slimakk/secured-vehicle-monitoring/Measurements/2023-05-21_18_19_influxdb_data.csv

#group | false | false | true | true | false | false | true | true
#datatype | string | long | dateTime:RFC3339 | dateTime:RFC3339 | dateTime:RFC3339 | double | string | string
#default | mean
 | result | table | _start | _stop | _time | _value | _field | _measurement
 |  | 0 | 2023-05-21T13:18:56.513924472Z | 2023-05-21T16:18:56.513924472Z | 2023-05-21T13:33:00Z | 29 | coolant_temp | OBD
 |  | 0 | 2023-05-21T13:18:56.513924472Z | 2023-05-21T16:18:56.513924472Z | 2023-05-21T13:34:00Z | 29 | coolant_temp | OBD
 |  | 0 | 2023-05-21T13:18:56.513924472Z | 2023-05-21T16:18:56.513924472Z | 2023-05-21T13:35:00Z | 29 | coolant_temp | OBD
 |  | 0 | 2023-05-21T13:18:56.513924472Z | 2023-05-21T16:18:56.513924472Z | 2023-05-21T13:36:00Z | 29 | coolant_temp | OBD
 |  | 0 | 2023-05-21T13:18:56.513924472Z | 2023-05-21T16:18:56.513924472Z | 2023-05-21T14:40:00Z | 28 | coolant_temp | OBD
 |  | 0 | 2023-05-21T13:18:56.513924472Z | 2023-05-21T16:18:56.513924472Z | 2023-05-21T14:41:00Z | 31.8 | coolant_temp | OBD
 |  | 0 | 2023-05-21T13:18:56.513924472Z | 2023-05-21T16:18:56.513924472Z | 2023-05-21T14:42:00Z | 46.4 | coolant_temp | OBD
 |  | 0 | 2023-05-21T13:18:56.513924472Z | 2023-05-21T16:18:56.513924472Z | 2023-05-21T14:43:00Z | 57.333333333333336 | coolant_temp | OBD
 |  | 0 | 2023-05-21T13:18:56.513924472Z | 2023-05-21T16:18:56.513924472Z | 2023-05-21T14:44:00Z | 65.6 | coolant_temp | OBD
 |  | 0 | 2023-05-21T13:18:56.513924472Z | 2023-05-21T16:18:56.513924472Z | 2023-05-21T14:45:00Z | 73.2 | coolant_temp | OBD
 |  | 0 | 2023-05-21T13:18:56.513924472Z | 2023-05-21T16:18:56.513924472Z | 2023-05-21T14:46:00Z | 79 | coolant_temp | OBD
 |  | 0 | 2023-05-21T13:18:56.513924472Z | 2023-05-21T16:18:56.513924472Z | 2023-05-21T14:47:00Z | 84.5 | coolant_temp | OBD
 |  | 0 | 2023-05-21T13:18:56.513924472Z | 2023-05-21T16:18:56.513924472Z | 2023-05-21T14:48:00Z | 89.8 | coolant_temp | OBD
 |  | 0 | 2023-05-21T13:18:56.513924472Z | 2023-05-21T16:18:56.513924472Z | 2023-05-21T14:49:00Z | 89.25 | coolant_temp | OBD
 |  | 0 | 2023-05-21T13:18:56.513924472Z | 2023-05-21T16:18:56.513924472Z | 2023-05-21T14:50:00Z | 87.8 | coolant_temp | OBD
 |  | 0 | 2023-05-21T13:18:56.513924472Z | 2023-05-21T16:18:56.513924472Z | 2023-05-21T14:51:00Z | 87.33333333333333 | coolant_temp | OBD
 |  | 0 | 2023-05-21T13:18:56.513924472Z | 2023-05-21T16:18:56.513924472Z | 2023-05-21T14:52:00Z | 87.33333333333333 | coolant_temp | OBD
 |  | 0 | 2023-05-21T13:18:56.513924472Z | 2023-05-21T16:18:56.513924472Z | 2023-05-21T14:53:00Z | 89 | coolant_temp | OBD
 |  | 0 | 2023-05-21T13:18:56.513924472Z | 2023-05-21T16:18:56.513924472Z | 2023-05-21T14:54:00Z | 88.8 | coolant_temp | OBD
 |  | 0 | 2023-05-21T13:18:56.513924472Z | 2023-05-21T16:18:56.513924472Z | 2023-05-21T14:55:00Z | 88.8 | coolant_temp | OBD
 |  | 0 | 2023-05-21T13:18:56.513924472Z | 2023-05-21T16:18:56.513924472Z | 2023-05-21T14:56:00Z | 91.33333333333333 | coolant_temp | OBD
 |  | 0 | 2023-05-21T13:18:56.513924472Z | 2023-05-21T16:18:56.513924472Z | 2023-05-21T14:57:00Z | 92 | coolant_temp | OBD
 |  | 0 | 2023-05-21T13:18:56.513924472Z | 2023-05-21T16:18:56.513924472Z | 2023-05-21T14:58:00Z | 93 | coolant_temp | OBD
 |  | 0 | 2023-05-21T13:18:56.513924472Z | 2023-05-21T16:18:56.513924472Z | 2023-05-21T14:59:00Z | 91.8 | coolant_temp | OBD
 |  | 0 | 2023-05-21T13:18:56.513924472Z | 2023-05-21T16:18:56.513924472Z | 2023-05-21T15:00:00Z | 90 | coolant_temp | OBD
 |  | 0 | 2023-05-21T13:18:56.513924472Z | 2023-05-21T16:18:56.513924472Z | 2023-05-21T15:01:00Z | 89.75 | coolant_temp | OBD
 |  | 0 | 2023-05-21T13:18:56.513924472Z | 2023-05-21T16:18:56.513924472Z | 2023-05-21T15:02:00Z | 90 | coolant_temp | OBD
 |  | 0 | 2023-05-21T13:18:56.513924472Z | 2023-05-21T16:18:56.513924472Z | 2023-05-21T15:03:00Z | 90 | coolant_temp | OBD
 |  | 0 | 2023-05-21T13:18:56.513924472Z | 2023-05-21T16:18:56.513924472Z | 2023-05-21T15:04:00Z | 90 | coolant_temp | OBD
 |  | 0 | 2023-05-21T13:18:56.513924472Z | 2023-05-21T16:18:56.513924472Z | 2023-05-21T15:05:00Z | 89.6 | coolant_temp | OBD
 |  | 0 | 2023-05-21T13:18:56.513924472Z | 2023-05-21T16:18:56.513924472Z | 2023-05-21T15:06:00Z | 90.33333333333333 | coolant_temp | OBD
 |  | 0 | 2023-05-21T13:18:56.513924472Z | 2023-05-21T16:18:56.513924472Z | 2023-05-21T15:07:00Z | 92.5 | coolant_temp | OBD
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
 |  | 2 | 2023-05-21T13:18:56.513924472Z | 2023-05-21T16:18:56.513924472Z | 2023-05-21T15:56:00Z | 53.4 | vehicle_speed | OBD
 |  | 2 | 2023-05-21T13:18:56.513924472Z | 2023-05-21T16:18:56.513924472Z | 2023-05-21T15:57:00Z | 46 | vehicle_speed | OBD
