slimakk/secured-vehicle-monitoring/Measurements/2023-06-09_14_13_influxdb_data.csv

#group | false | false | true | true | false | false | true | true
#datatype | string | long | dateTime:RFC3339 | dateTime:RFC3339 | dateTime:RFC3339 | double | string | string
#default | mean
 | result | table | _start | _stop | _time | _value | _field | _measurement
 |  | 0 | 2023-05-10T12:12:42.571693991Z | 2023-06-09T12:12:42.571693991Z | 2023-05-21T14:39:20Z | 4913.9652 | lat | location
 |  | 0 | 2023-05-10T12:12:42.571693991Z | 2023-06-09T12:12:42.571693991Z | 2023-05-21T14:39:25Z | 4913.9652 | lat | location
 |  | 0 | 2023-05-10T12:12:42.571693991Z | 2023-06-09T12:12:42.571693991Z | 2023-05-21T14:39:50Z | 4913.9652 | lat | location
 |  | 0 | 2023-05-10T12:12:42.571693991Z | 2023-06-09T12:12:42.571693991Z | 2023-05-21T14:40:05Z | 4913.9635 | lat | location
 |  | 0 | 2023-05-10T12:12:42.571693991Z | 2023-06-09T12:12:42.571693991Z | 2023-05-21T14:40:15Z | 4913.9636 | lat | location
 |  | 0 | 2023-05-10T12:12:42.571693991Z | 2023-06-09T12:12:42.571693991Z | 2023-05-21T14:40:30Z | 4913.9636 | lat | location
 |  | 0 | 2023-05-10T12:12:42.571693991Z | 2023-06-09T12:12:42.571693991Z | 2023-05-21T14:40:45Z | 4913.9636 | lat | location
 |  | 0 | 2023-05-10T12:12:42.571693991Z | 2023-06-09T12:12:42.571693991Z | 2023-05-21T14:40:50Z | 4913.9556 | lat | location
 |  | 0 | 2023-05-10T12:12:42.571693991Z | 2023-06-09T12:12:42.571693991Z | 2023-05-21T14:41:00Z | 4913.9556 | lat | location
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
 |  | 1 | 2023-05-10T12:12:42.571693991Z | 2023-06-09T12:12:42.571693991Z | 2023-05-21T15:55:20Z | 1630.2676 | lon | location
 |  | 1 | 2023-05-10T12:12:42.571693991Z | 2023-06-09T12:12:42.571693991Z | 2023-05-21T15:55:40Z | 1630.2676 | lon | location
 |  | 1 | 2023-05-10T12:12:42.571693991Z | 2023-06-09T12:12:42.571693991Z | 2023-05-21T15:55:50Z | 1630.2676 | lon | location
 |  | 1 | 2023-05-10T12:12:42.571693991Z | 2023-06-09T12:12:42.571693991Z | 2023-05-21T15:55:55Z | 1630.5488 | lon | location
 |  | 1 | 2023-05-10T12:12:42.571693991Z | 2023-06-09T12:12:42.571693991Z | 2023-05-21T15:56:10Z | 1630.5471 | lon | location
 |  | 1 | 2023-05-10T12:12:42.571693991Z | 2023-06-09T12:12:42.571693991Z | 2023-05-21T15:56:40Z | 1630.5471 | lon | location
