slimakk/secured-vehicle-monitoring/Schematic/new/final/iot_diagnostic_tool-car_comm.pdf

File: car.kicad_sch Sheet: /car_comm/ FEKT VUT GND

Id: 5/8 Title: OBD Monitoring Device
