slimakk/secured-vehicle-monitoring/Schematic/new/final/iot_diagnostic_tool-connectors.pdf

File: connect.kicad_sch Sheet: /connectors/ FEKT VUT

Id: 4/8 Title: OBD Monitoring Device
