slimakk/secured-vehicle-monitoring/Schematic/new/final/iot_diagnostic_tool-iot_module-antenna.pdf

File: ant.kicad_sch Sheet: /iot_module/antenna/ FEKT VUT C40 NM

Id: 8/8 Title: OBD Monitoring Device
