slimakk/secured-vehicle-monitoring/Schematic/new/final/iot_diagnostic_tool-iot_module-sim.pdf

Id: 6/8 Title: OBD Monitoring Device
