slimakk/secured-vehicle-monitoring/Schematic/new/final/iot_diagnostic_tool-iot_module-usb.pdf

File: usb.kicad_sch Sheet: /iot_module/usb/ FEKT VUT

Id: 7/8 Title: OBD Monitoring Device
