slimakk/secured-vehicle-monitoring/Schematic/new/final/iot_diagnostic_tool-iot_module.pdf

File: iot.kicad_sch Sheet: /iot_module/ FEKT VUT

Id: 3/8 Title: OBD Monitoring Device
