slimakk/secured-vehicle-monitoring/Schematic/new/final/iot_diagnostic_tool-power_supply.pdf

File: pwr.kicad_sch Sheet: /power_supply/ FEKT VUT

Id: 2/8 Title: OBD Monitoring Device
