slimakk/secured-vehicle-monitoring/Schematic/new/new_layout.pdf

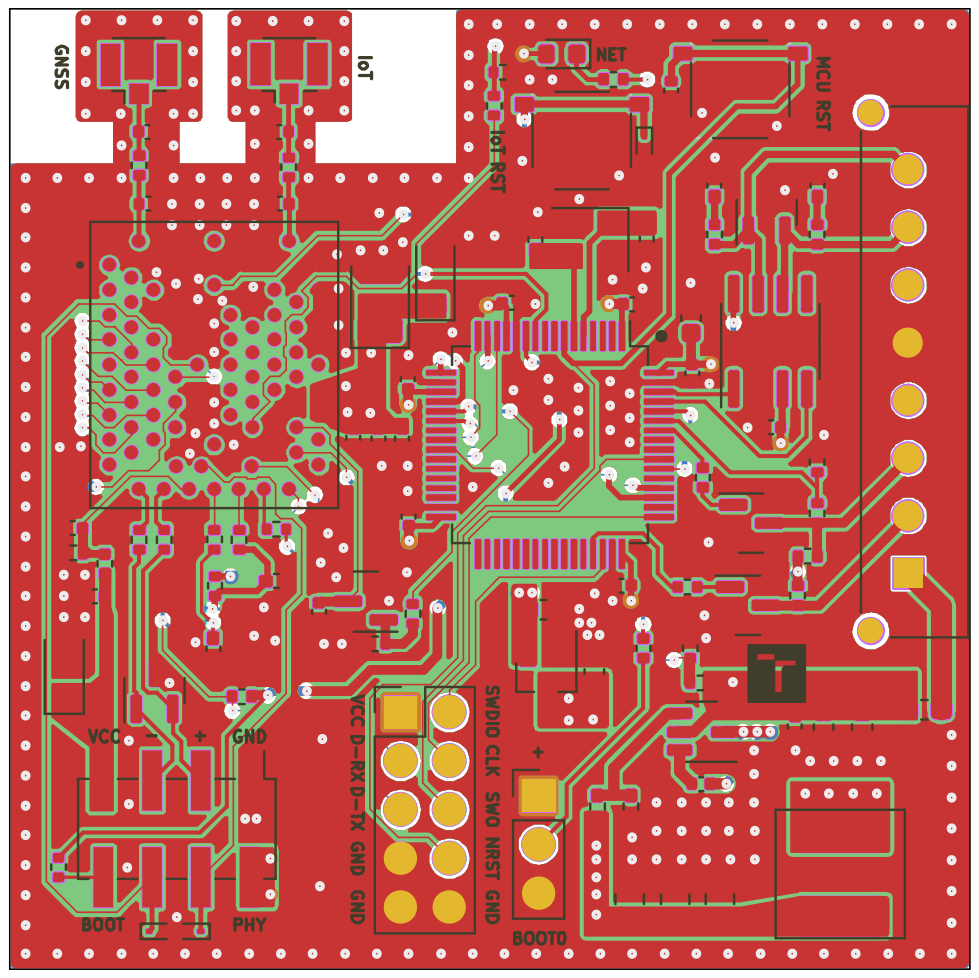
[picture p37: page 1]
