slimakk/secured-vehicle-monitoring/Schematic/new/new_layout_cut.pdf

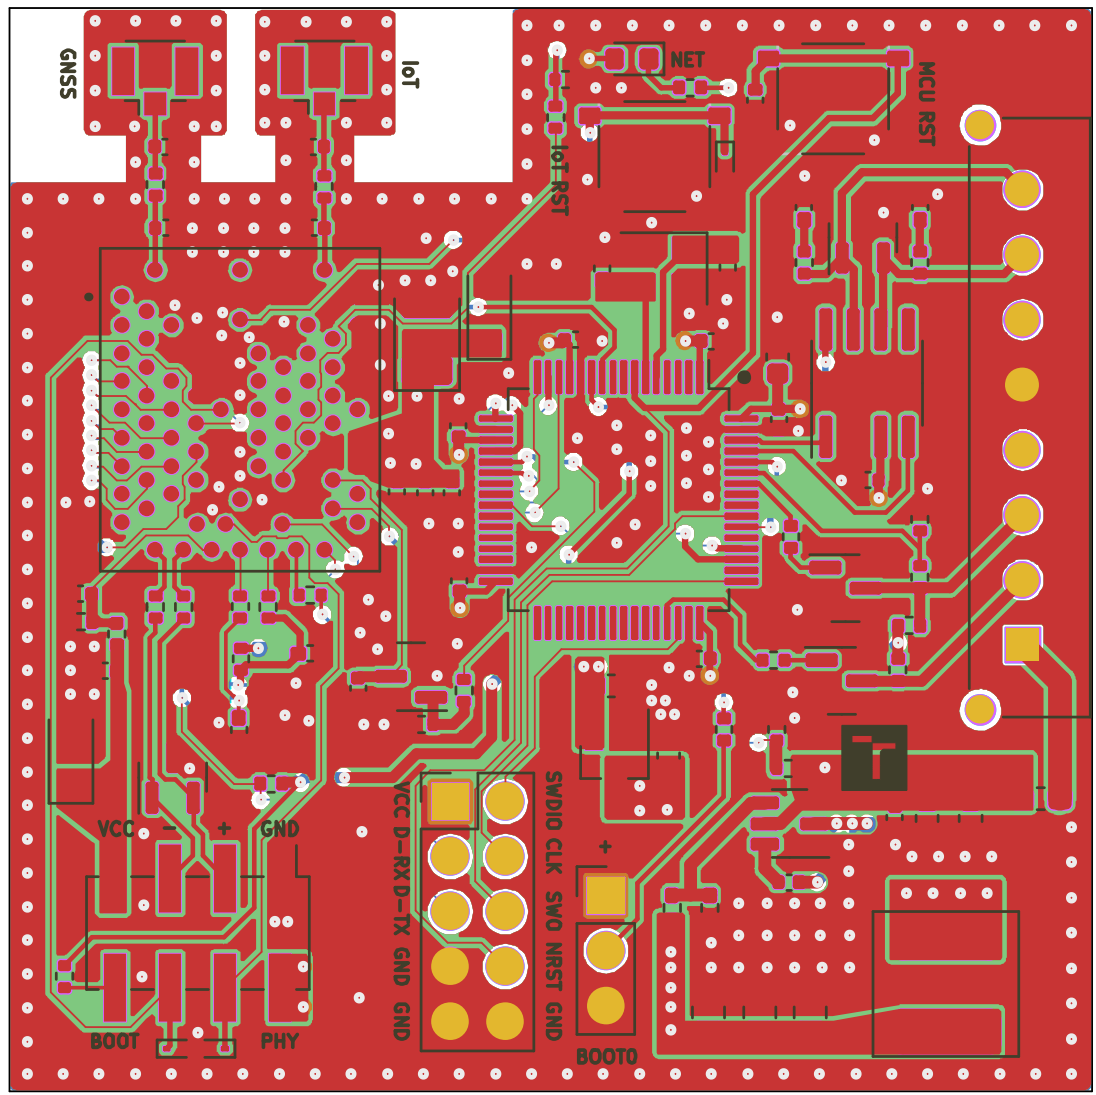
[picture p38: page 1]
