slimakk/secured-vehicle-monitoring/Schematic/new/pontrig.pdf

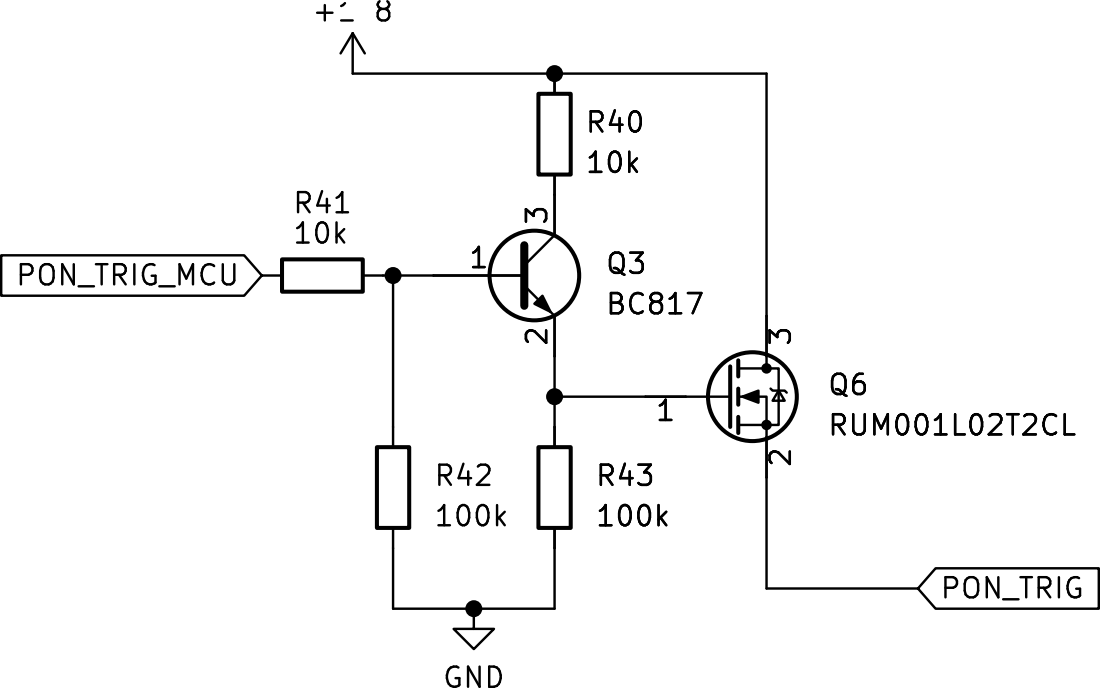
[picture p39: page 1]
