slimakk/secured-vehicle-monitoring/Schematic/new/pwr.pdf

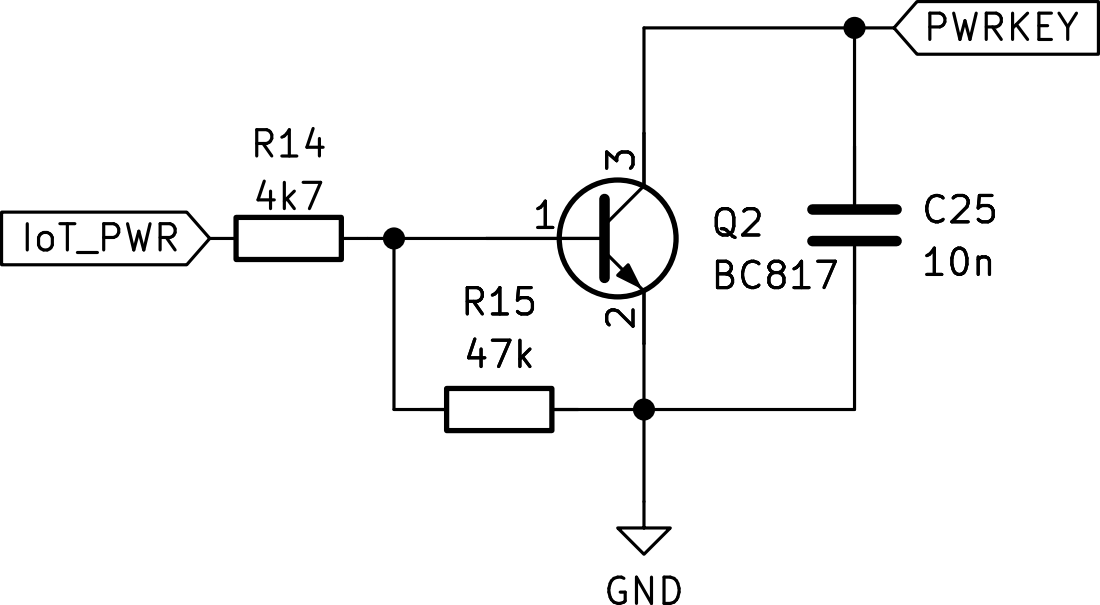
[picture p40: page 1]
