slimakk/secured-vehicle-monitoring/Schematic/new/pwr_sup.pdf

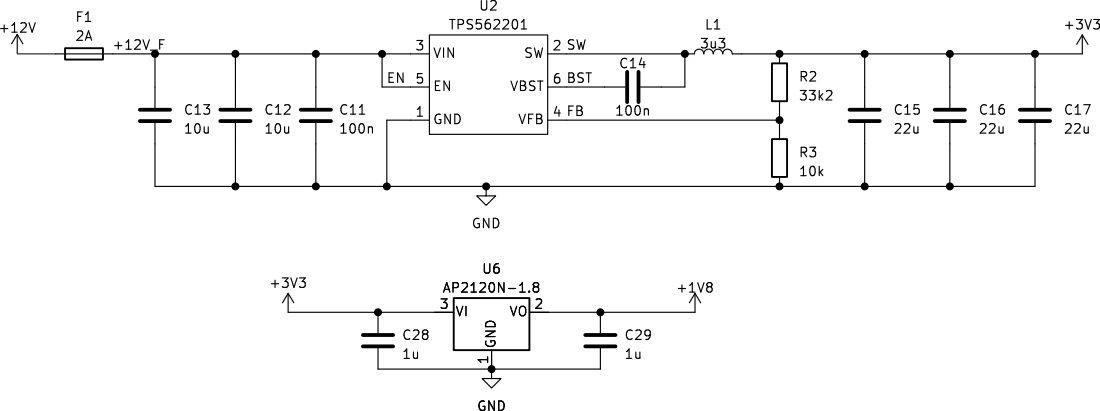
[picture p41: page 1]
