slimakk/secured-vehicle-monitoring/Schematic/new/sim.pdf

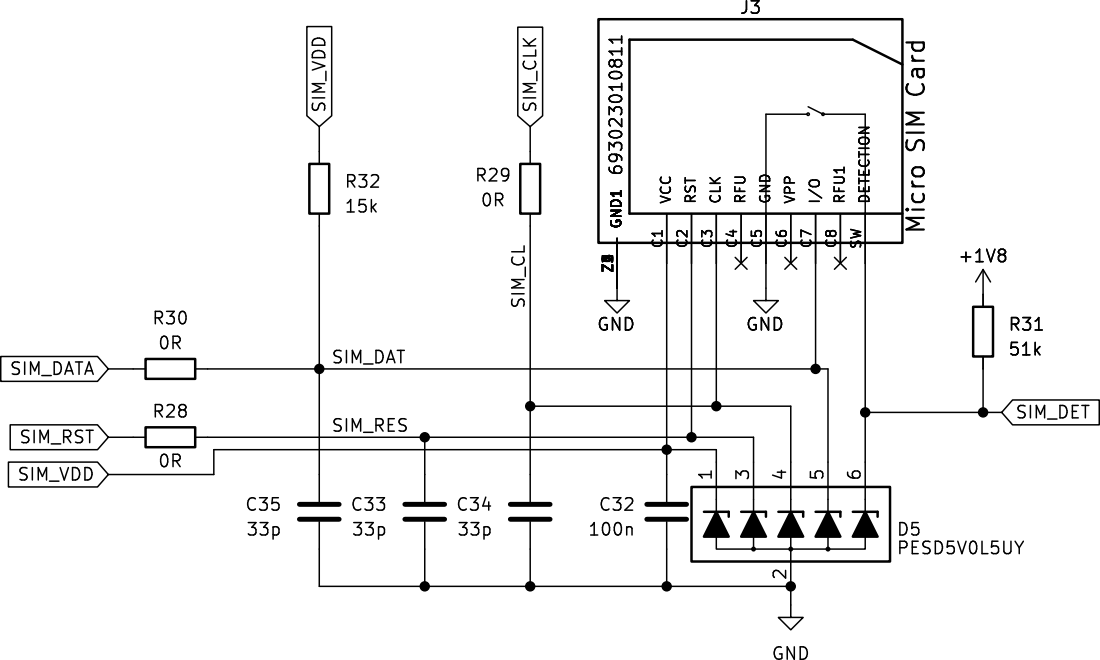
[picture p42: page 1]
