slimakk/secured-vehicle-monitoring/Schematic/new/usb.pdf

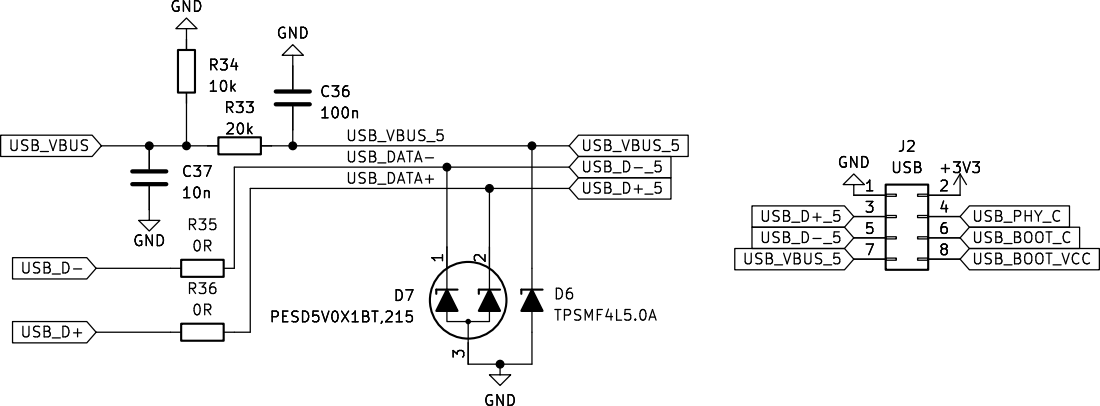
[picture p43: page 1]
