slimakk/secured-vehicle-monitoring/Schematic/part/stm_v3-Power Supply.pdf

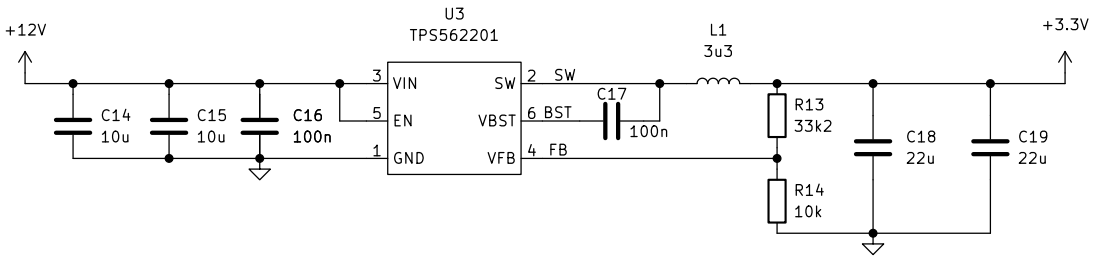
[picture p44: page 1]
