slimakk/secured-vehicle-monitoring/Schematic/schema_v1.pdf

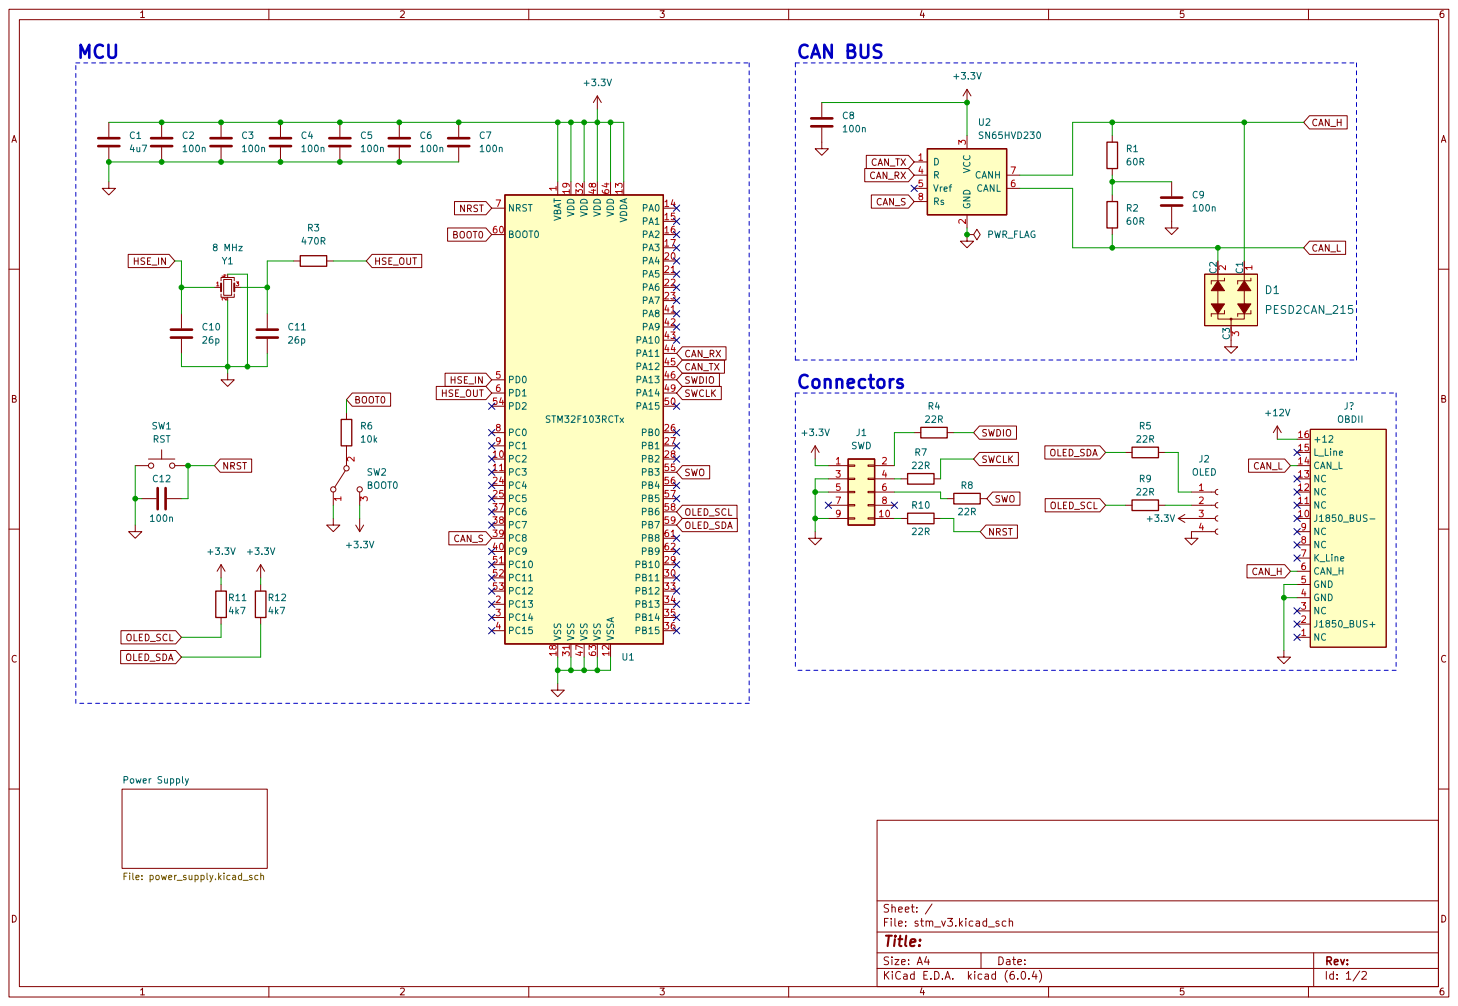
[picture p45: page 1]

1 PC2 10 PC3 11 VSSA 12 VDDA 13 PA0 14 PA1 15 PA2 16 PA3 17 VSS 18 VDD 19 PC13 2 PA4 20 PA5 21 PA6 22 PA7 23 PC4 24 PC5 25 PB0 26 PB1 27 PB2 28 PB10 29 PC14 3 PB11 30 VSS 31 VDD 32 PB12 33 PB13 34 PB14 35 PB15 36 PC6 37 PC7 38 PC8 39 PC15 4 PC9 40 PA8 41 PA9 42 PA10 43 PA11 44 PA12 45 PA13 46 VSS 47 VDD 48 PA14 49 PD0 5 PA15 50 PC10 51 PC11 52 PC12 53 PD2 54 PB3 55 PB4 56 PB5 57 PB6 58 PB7 59 PD1 6 BOOT0 60 PB8 61 PB9 62 VSS 63 VDD 64 NRST 7 PC0 8 PC1 9 U1 STM32F103RCTx PWR_FLAG

File: stm_v3.kicad_sch Sheet: / Power Supply

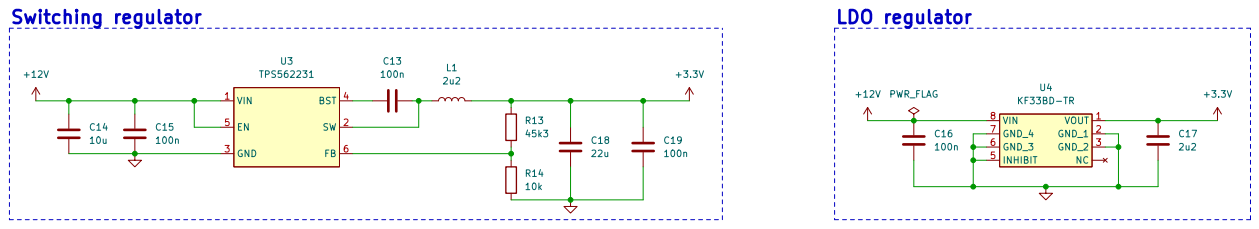
[picture p46: page 2]
