slimakk/secured-vehicle-monitoring/iot_obd_monitoring_device/Core/Src/tim.c

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
/* Includes ------------------------------------------------------------------*/
#include "tim.h"

/* USER CODE BEGIN 0 */
extern OBD obd_comm;
extern BG77 module;
/* USER CODE END 0 */

TIM_HandleTypeDef htim6;
TIM_HandleTypeDef htim7;
TIM_HandleTypeDef htim16;

/* TIM6 init function */
void MX_TIM6_Init(void)
{

  TIM_MasterConfigTypeDef sMasterConfig = {0};

  htim6.Instance = TIM6;
  htim6.Init.Prescaler = 800;
  htim6.Init.CounterMode = TIM_COUNTERMODE_UP;
  htim6.Init.Period = 8000;
  htim6.Init.AutoReloadPreload = TIM_AUTORELOAD_PRELOAD_DISABLE;
  if (HAL_TIM_Base_Init(&htim6) != HAL_OK)
  {
    Error_Handler();
  }
  sMasterConfig.MasterOutputTrigger = TIM_TRGO_RESET;
  sMasterConfig.MasterSlaveMode = TIM_MASTERSLAVEMODE_DISABLE;
  if (HAL_TIMEx_MasterConfigSynchronization(&htim6, &sMasterConfig) != HAL_OK)
  {
    Error_Handler();
  }
}
/* TIM7 init function */
void MX_TIM7_Init(void)
{

  TIM_MasterConfigTypeDef sMasterConfig = {0};

  htim7.Instance = TIM7;
  htim7.Init.Prescaler = 39999;
  htim7.Init.CounterMode = TIM_COUNTERMODE_UP;
  htim7.Init.Period = 1999;
  htim7.Init.AutoReloadPreload = TIM_AUTORELOAD_PRELOAD_DISABLE;
  if (HAL_TIM_Base_Init(&htim7) != HAL_OK)
  {
    Error_Handler();
  }
  sMasterConfig.MasterOutputTrigger = TIM_TRGO_RESET;
  sMasterConfig.MasterSlaveMode = TIM_MASTERSLAVEMODE_DISABLE;
  if (HAL_TIMEx_MasterConfigSynchronization(&htim7, &sMasterConfig) != HAL_OK)
  {
    Error_Handler();
  }
}
/* TIM16 init function */
void MX_TIM16_Init(void)
{

  htim16.Instance = TIM16;
  htim16.Init.Prescaler = 39999;
  htim16.Init.CounterMode = TIM_COUNTERMODE_UP;
  htim16.Init.Period = 3999;
  htim16.Init.ClockDivision = TIM_CLOCKDIVISION_DIV1;
  htim16.Init.RepetitionCounter = 0;
  htim16.Init.AutoReloadPreload = TIM_AUTORELOAD_PRELOAD_DISABLE;
  if (HAL_TIM_Base_Init(&htim16) != HAL_OK)
  {
    Error_Handler();
  }
}

void HAL_TIM_Base_MspInit(TIM_HandleTypeDef* tim_baseHandle)
{

  if(tim_baseHandle->Instance==TIM6)
  {
    /* TIM6 clock enable */
    __HAL_RCC_TIM6_CLK_ENABLE();

    /* TIM6 interrupt Init */
    HAL_NVIC_SetPriority(TIM6_DAC_IRQn, 2, 0);
    HAL_NVIC_EnableIRQ(TIM6_DAC_IRQn);
  }
  else if(tim_baseHandle->Instance==TIM7)
  {
    /* TIM7 clock enable */
    __HAL_RCC_TIM7_CLK_ENABLE();

    /* TIM7 interrupt Init */
    HAL_NVIC_SetPriority(TIM7_IRQn, 2, 0);
    HAL_NVIC_EnableIRQ(TIM7_IRQn);
  }
  else if(tim_baseHandle->Instance==TIM16)
  {
    /* TIM16 clock enable */
    __HAL_RCC_TIM16_CLK_ENABLE();

    /* TIM16 interrupt Init */
    HAL_NVIC_SetPriority(TIM1_UP_TIM16_IRQn, 2, 0);
    HAL_NVIC_EnableIRQ(TIM1_UP_TIM16_IRQn);
  }
}

void HAL_TIM_Base_MspDeInit(TIM_HandleTypeDef* tim_baseHandle)
{

  if(tim_baseHandle->Instance==TIM6)
  {
    /* Peripheral clock disable */
    __HAL_RCC_TIM6_CLK_DISABLE();

    /* TIM6 interrupt Deinit */
    HAL_NVIC_DisableIRQ(TIM6_DAC_IRQn);
  }
  else if(tim_baseHandle->Instance==TIM7)
  {
    /* Peripheral clock disable */
    __HAL_RCC_TIM7_CLK_DISABLE();

    /* TIM7 interrupt Deinit */
    HAL_NVIC_DisableIRQ(TIM7_IRQn);
  }
  else if(tim_baseHandle->Instance==TIM16)
  {
    /* Peripheral clock disable */
    __HAL_RCC_TIM16_CLK_DISABLE();

    /* TIM16 interrupt Deinit */
    HAL_NVIC_DisableIRQ(TIM1_UP_TIM16_IRQn);
  }
}

/* USER CODE BEGIN 1 */
void HAL_TIM_PeriodElapsedCallback(TIM_HandleTypeDef *htim)
{
	if (htim->Instance == TIM2)
	{
	    HAL_IncTick();
	}
	if(htim->Instance == TIM6)
	{
		if(obd_comm.msg_type == 0)
		{
			__NOP();
		}
		else
		{
			obd_comm.msg_type = 3;
		}
		HAL_TIM_Base_Stop_IT(htim);
	}
	else if(htim->Instance == TIM7)
	{
		module.received = 1;
		HAL_TIM_Base_Stop_IT(htim);
	}
	else if(htim->Instance == TIM16)
	{
		obd_comm.timeout = 1;
		HAL_TIM_Base_Stop_IT(htim);
	}
}


/* USER CODE END 1 */
