slimakk/secured-vehicle-monitoring/iot_obd_monitoring_device/Core/Src/OBD/can.c

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
/* Includes ------------------------------------------------------------------*/
#include "can.h"
#include "OBD.h"
/* USER CODE BEGIN 0 */
extern OBD obd_comm;
//extern IWDG_HandleTypeDef hiwdg;
uint32_t tx_mailbox;
uint8_t rx_mailbox[RX_DATA_LENGTH];

/* USER CODE END 0 */

CAN_HandleTypeDef hcan1;

/* CAN1 init function */
void MX_CAN1_Init(void)
{

  hcan1.Instance = CAN1;
  hcan1.Init.Prescaler = 16;
  hcan1.Init.Mode = CAN_MODE_NORMAL;
  hcan1.Init.SyncJumpWidth = CAN_SJW_1TQ;
  hcan1.Init.TimeSeg1 = CAN_BS1_8TQ;
  hcan1.Init.TimeSeg2 = CAN_BS2_1TQ;
  hcan1.Init.TimeTriggeredMode = DISABLE;
  hcan1.Init.AutoBusOff = DISABLE;
  hcan1.Init.AutoWakeUp = DISABLE;
  hcan1.Init.AutoRetransmission = DISABLE;
  hcan1.Init.ReceiveFifoLocked = DISABLE;
  hcan1.Init.TransmitFifoPriority = DISABLE;
  if (HAL_CAN_Init(&hcan1) != HAL_OK)
  {
    Error_Handler();
  }
}

void HAL_CAN_MspInit(CAN_HandleTypeDef* canHandle)
{

  GPIO_InitTypeDef GPIO_InitStruct = {0};
  if(canHandle->Instance==CAN1)
  {
    /* CAN1 clock enable */
    __HAL_RCC_CAN1_CLK_ENABLE();

    __HAL_RCC_GPIOB_CLK_ENABLE();
    /**CAN1 GPIO Configuration
    PB8     ------> CAN1_RX
    PB9     ------> CAN1_TX
    */
    GPIO_InitStruct.Pin = GPIO_PIN_8|GPIO_PIN_9;
    GPIO_InitStruct.Mode = GPIO_MODE_AF_PP;
    GPIO_InitStruct.Pull = GPIO_NOPULL;
    GPIO_InitStruct.Speed = GPIO_SPEED_FREQ_VERY_HIGH;
    GPIO_InitStruct.Alternate = GPIO_AF9_CAN1;
    HAL_GPIO_Init(GPIOB, &GPIO_InitStruct);

    /* CAN1 interrupt Init */
    HAL_NVIC_SetPriority(CAN1_RX0_IRQn, 0, 0);
    HAL_NVIC_EnableIRQ(CAN1_RX0_IRQn);
    HAL_NVIC_SetPriority(CAN1_RX1_IRQn, 0, 0);
    HAL_NVIC_EnableIRQ(CAN1_RX1_IRQn);
  }
}

void HAL_CAN_MspDeInit(CAN_HandleTypeDef* canHandle)
{

  if(canHandle->Instance==CAN1)
  {
    /* Peripheral clock disable */
    __HAL_RCC_CAN1_CLK_DISABLE();

    /**CAN1 GPIO Configuration
    PB8     ------> CAN1_RX
    PB9     ------> CAN1_TX
    */
    HAL_GPIO_DeInit(GPIOB, GPIO_PIN_8|GPIO_PIN_9);

    /* CAN1 interrupt Deinit */
    HAL_NVIC_DisableIRQ(CAN1_RX0_IRQn);
    HAL_NVIC_DisableIRQ(CAN1_RX1_IRQn);
  }
}

/* USER CODE BEGIN 1 */
void can_config(void)
{
	CAN_FilterTypeDef can_filter;
	can_filter.FilterBank = 0;
	can_filter.FilterMode = CAN_FILTERMODE_IDMASK;
	can_filter.FilterScale = CAN_FILTERSCALE_32BIT;
	can_filter.FilterIdHigh = 0x7E8 << 5;
	can_filter.FilterIdLow = 0x0000;
	can_filter.FilterMaskIdHigh = 0x7F8 << 5;
	can_filter.FilterMaskIdLow = 0x0000;
	can_filter.FilterFIFOAssignment = CAN_RX_FIFO0;
	can_filter.FilterActivation = ENABLE;

	if(HAL_CAN_ConfigFilter(&hcan1, &can_filter) != HAL_OK)
	{
		Error_Handler();
	}

	if(HAL_CAN_Start(&hcan1) != HAL_OK)
	{
		Error_Handler();
	}
	HAL_CAN_ActivateNotification(&hcan1, CAN_IT_RX_FIFO0_MSG_PENDING);
}
/*
 * @brief	Sends a message via ISO 15765 CAN
 * @param	*tx_frame	Pointer to the requested TX frame
 * @retval	TRUE if valid message has been received, else FALSE
 * */
uint8_t can_send_msg(uint8_t *tx_frame)
{
	CAN_TxHeaderTypeDef tx_header;
	tx_header.StdId = 0x7DF;
	tx_header.DLC = TX_DATA_LENGTH;
	tx_header.IDE = CAN_ID_STD;
	tx_header.RTR = CAN_RTR_DATA;

	obd_comm.msg_type = 1;
	HAL_TIM_Base_Start_IT(MSG_TIMER);
	if(HAL_CAN_AddTxMessage(&hcan1, &tx_header, tx_frame, &tx_mailbox) != HAL_OK)
	{
		Error_Handler();
	}
	while((obd_comm.msg_type != 0) && (obd_comm.timeout != 1))
	{
		__NOP();
	}
	if(obd_comm.timeout == 1)
	{
		obd_comm.timeout = 0;
		return (FALSE);
	}
	obd_comm.current_value = obd2_pid_parse(rx_mailbox);
	return (TRUE);
}
/*
 * @brief	CAN receive callback function
 * @param	hcan	CAN handle
 * @retval	None
 * */
void HAL_CAN_RxFifo0MsgPendingCallback(CAN_HandleTypeDef *hcan)
{
	CAN_RxHeaderTypeDef rx_header;

	obd_comm.msg_type = 0;

	HAL_CAN_GetRxMessage(&hcan1, CAN_RX_FIFO0, &rx_header, rx_mailbox);

	HAL_TIM_Base_Stop_IT(MSG_TIMER);

//	HAL_IWDG_Refresh(&hiwdg);
}

void HAL_CAN_ErrorCallback(CAN_HandleTypeDef *hcan)
{
	__HAL_CAN_CLEAR_FLAG(hcan, CAN_FLAG_FOV0);
}

/* USER CODE END 1 */
