slimakk/secured-vehicle-monitoring/obd_monitoring_device/Core/Src/it_callbacks.c

/*
 * it_callbacks.c
 *
 *  Created on: Feb 15, 2023
 *      Author: Miro
 */
#include "it_callbacks.h"
#include "OBD_PID.h"

extern TIM_HandleTypeDef htim1;
extern TIM_HandleTypeDef htim6;
extern OBD obd_comm;

void HAL_TIM_PeriodElapsedCallback(TIM_HandleTypeDef *htim)
{
	if(htim->Instance == TIM1)
	{
		if(HAL_GPIO_ReadPin(MENU_BTN_GPIO_Port, MENU_BTN_Pin)== GPIO_PIN_SET)
		{
			obd_comm.button_state = 1;
			if(obd_comm.pid_index == 89)
			{
				obd_comm.pid_index = 0;
			}
			else
			{
				obd_comm.pid_index++;
			}
			obd_comm.pid = Get_PID(obd_comm.pid_index);
			HAL_TIM_Base_Stop_IT(&htim1);
		}
	}
	if(htim->Instance == TIM6)
	{
		if(obd_comm.msg_type == 0)
		{
			__NOP();
		}
		else
			obd_comm.msg_type = 3;
		HAL_TIM_Base_Stop_IT(&htim6);
	}
}
